kemptm/NCNCA-Lap-Counter/doc/images/Arduino MEGA 2560 Sheet 1.png

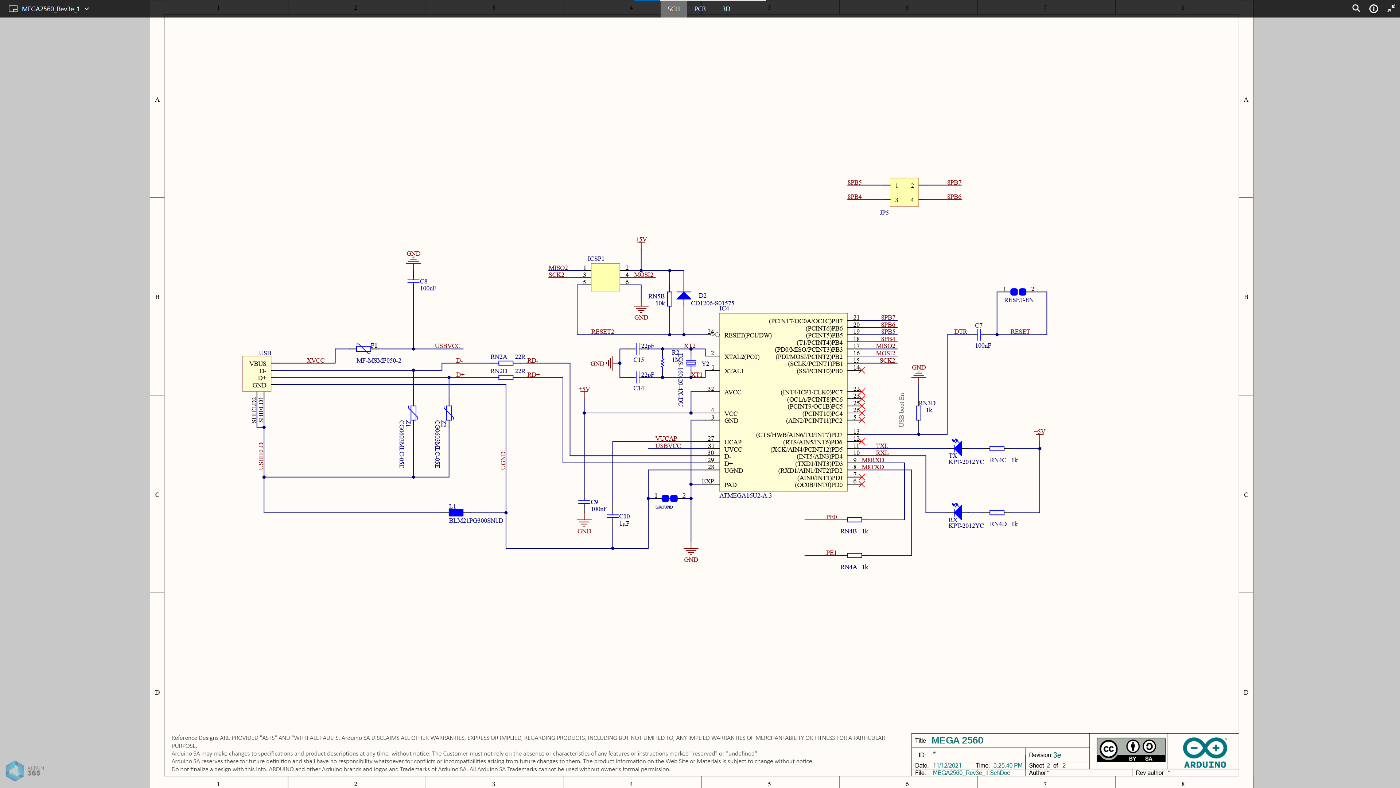
doc/images/Arduino MEGA 2560 Sheet 1.png
