kemptm/NCNCA-Lap-Counter/doc/images/Arduino MEGA 2560 Sheet 2.png

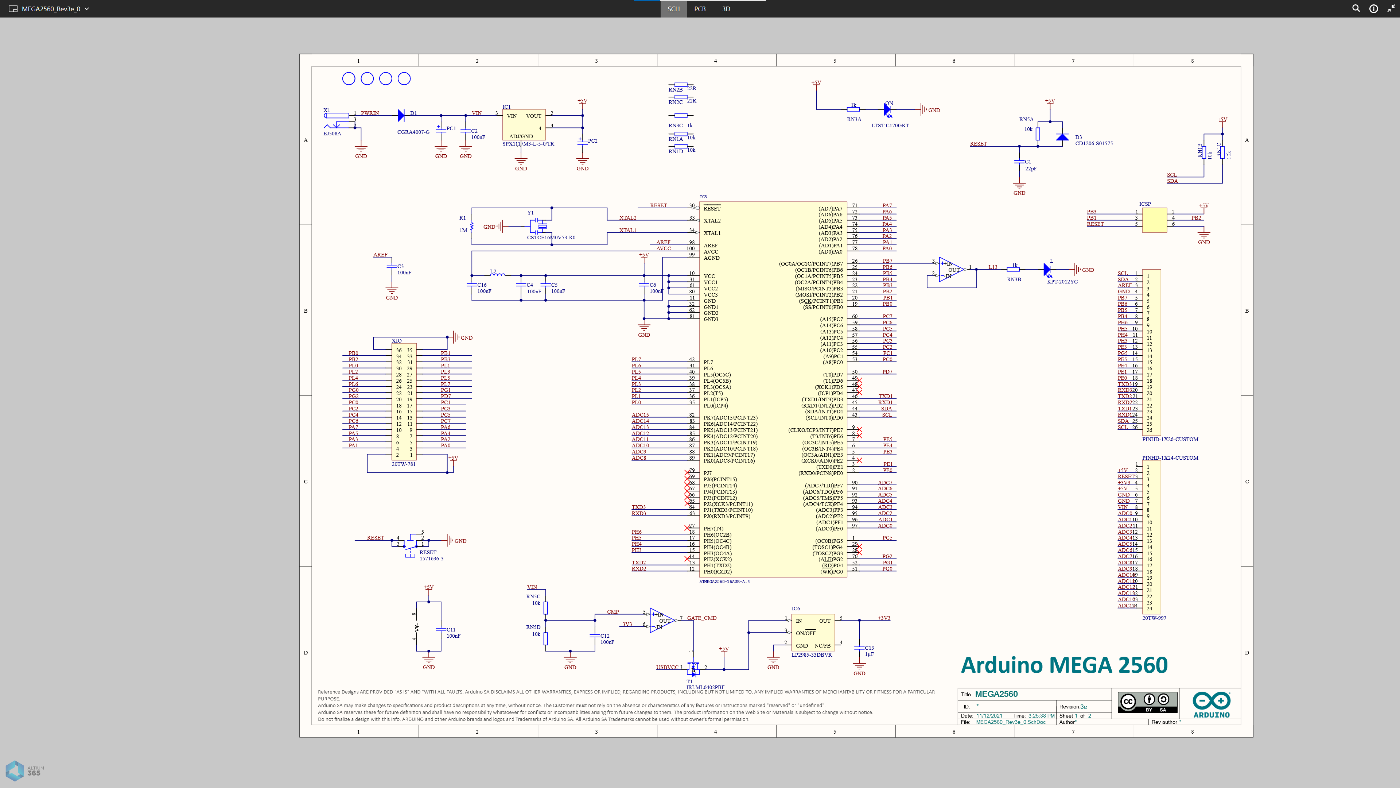
doc/images/Arduino MEGA 2560 Sheet 2.png
