kemptm/NCNCA-Lap-Counter/doc/images/PXL_20230830_222036066.jpg

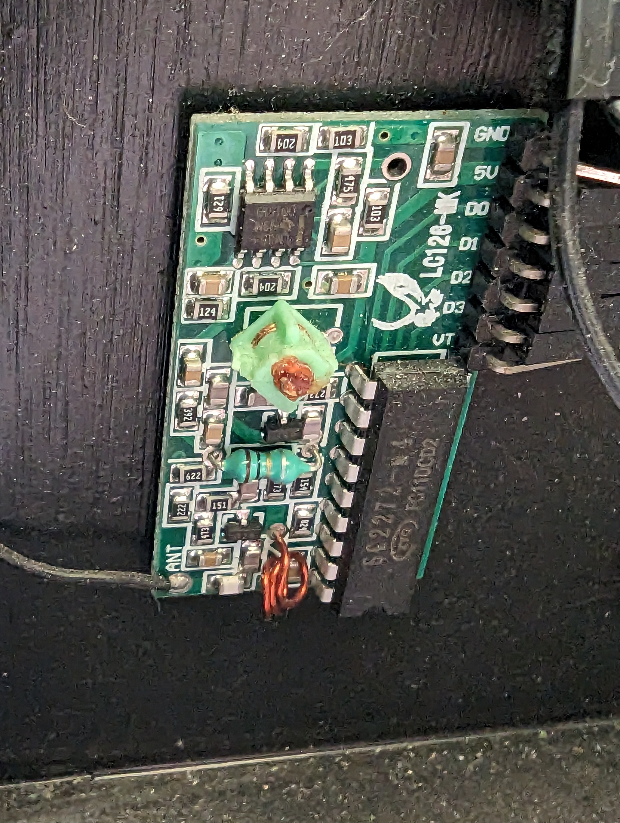
doc/images/PXL_20230830_222036066.jpg
