kemptm/NCNCA-Lap-Counter/doc/images/PXL_20230830_223550689.jpg

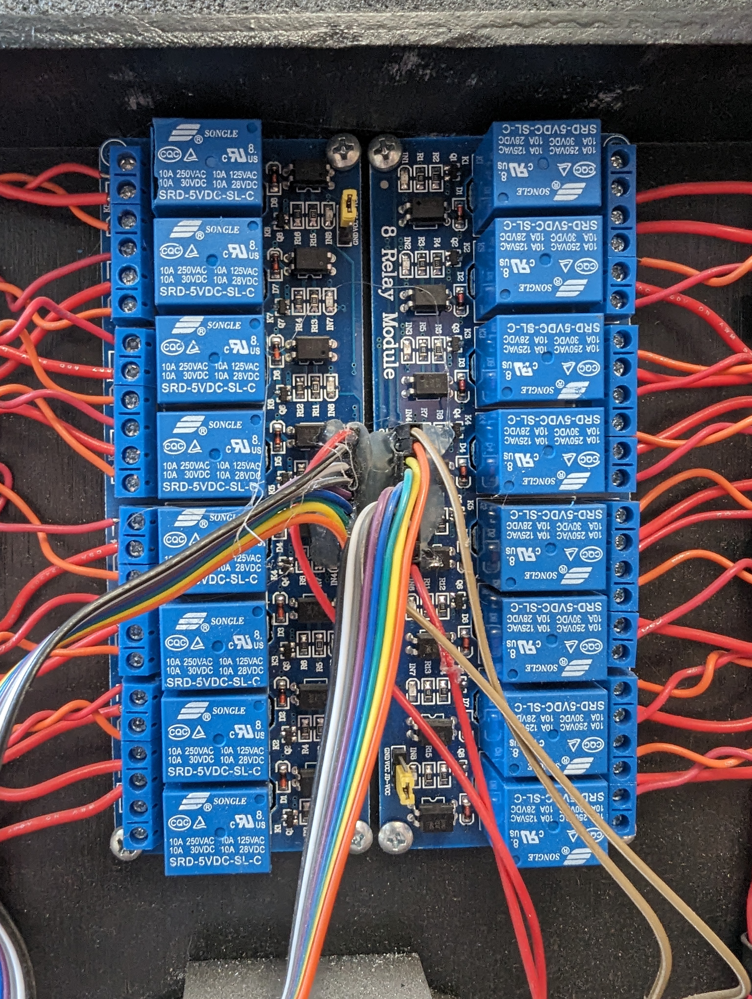
doc/images/PXL_20230830_223550689.jpg
