kemptm/NCNCA-Lap-Counter/doc/images/PXL_20230830_223600172.jpg

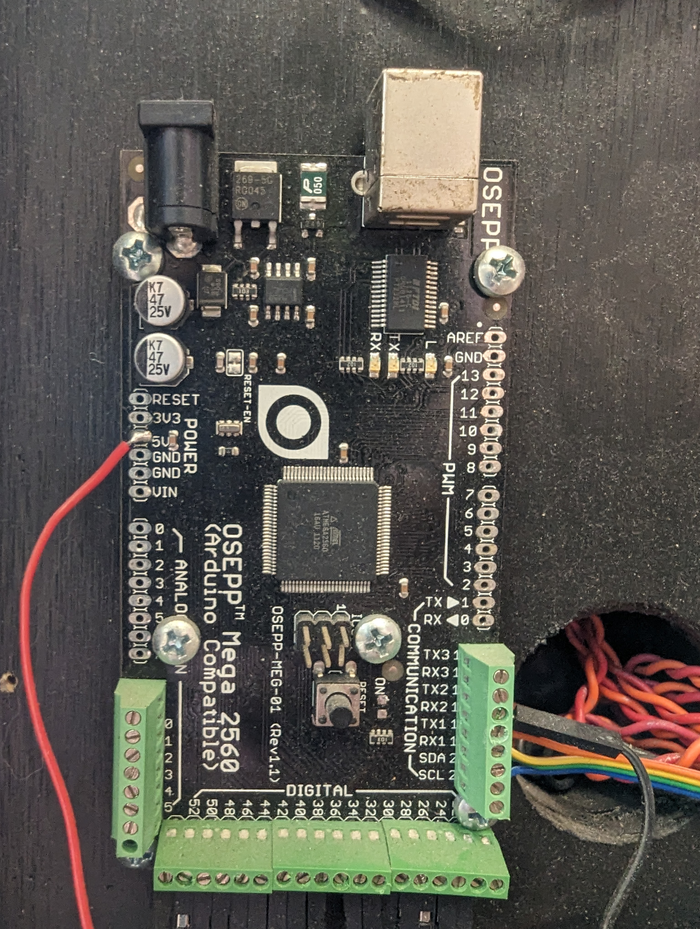
doc/images/PXL_20230830_223600172.jpg
