kemptm/NCNCA-Lap-Counter/doc/images/PXL_20230830_223612654.jpg

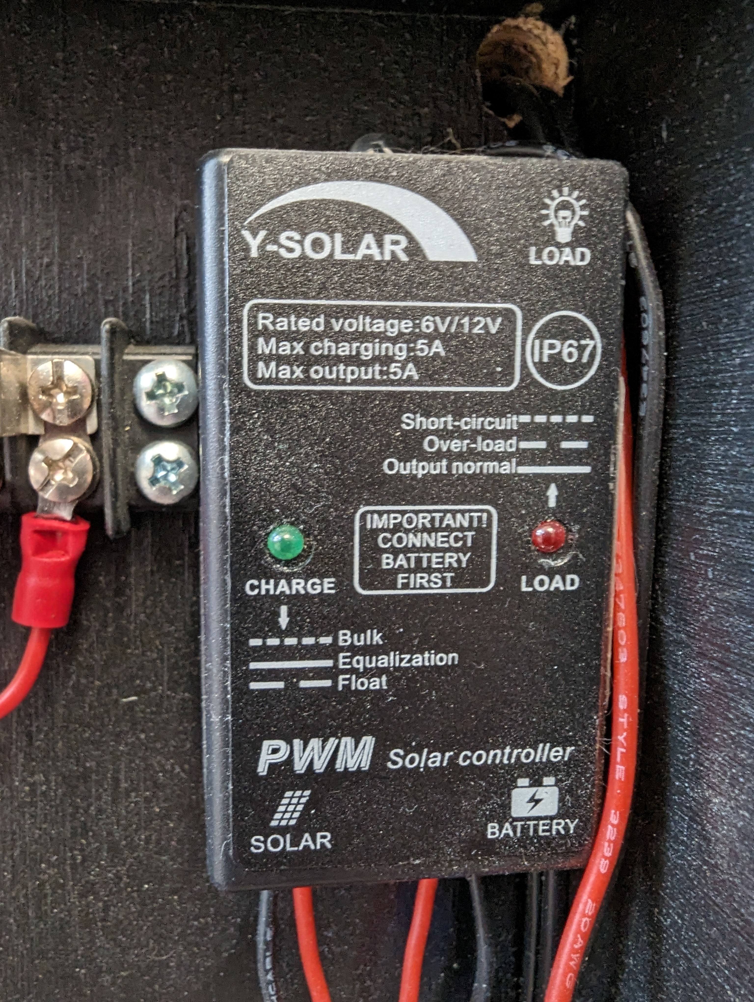
doc/images/PXL_20230830_223612654.jpg
