kemptm/NCNCA-Lap-Counter/doc/images/PXL_20230830_223639269.jpg

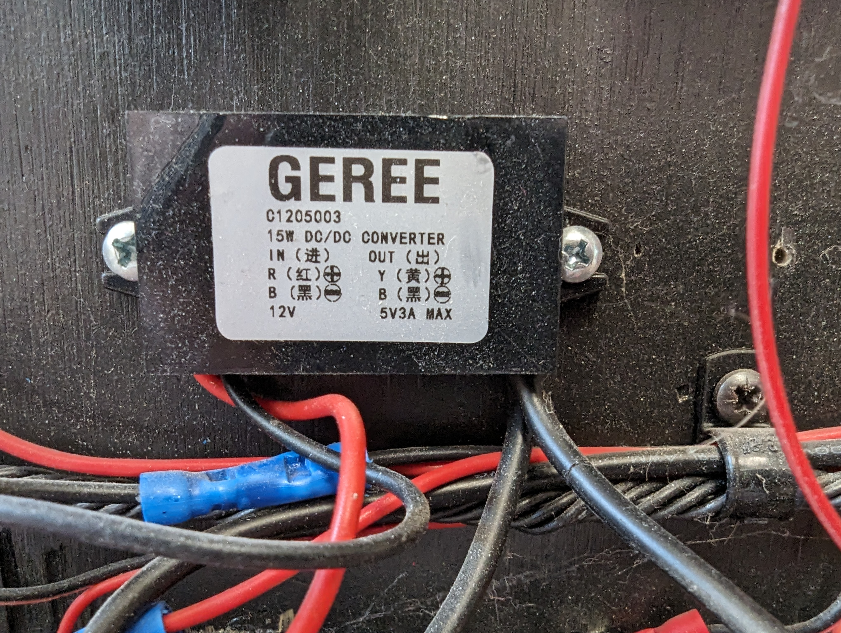
doc/images/PXL_20230830_223639269.jpg
