kemptm/NCNCA-Lap-Counter/mechanical/8-Barrier-Strip.FCStd

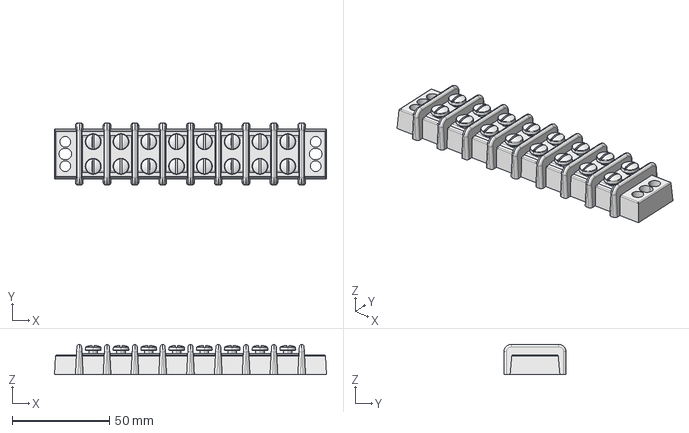
[picture p46: CAD file, 2024-01-13]
mechanical/8-Barrier-Strip.FCStd
139.9 x 32.0 x 15.5 mm
