kemptm/NCNCA-Lap-Counter/mechanical/Flyback-Board.FCStd

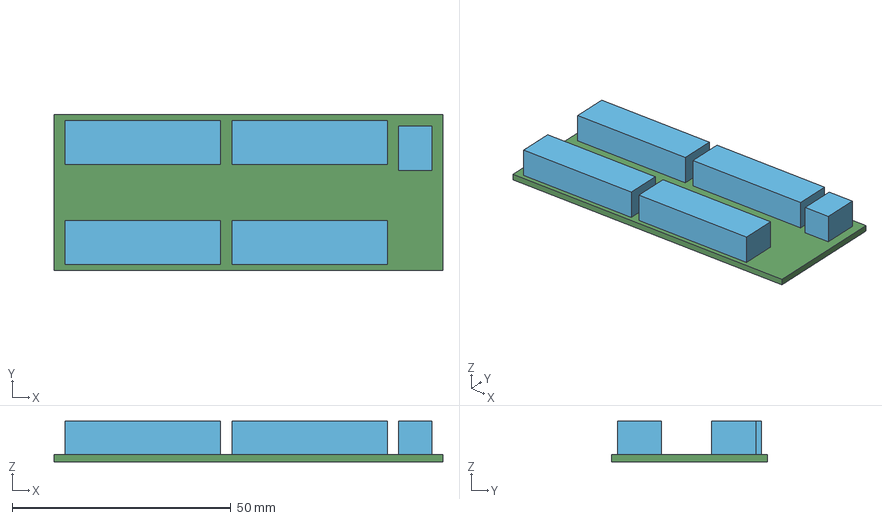
[picture p47: CAD file, 2024-01-13]
mechanical/Flyback-Board.FCStd
88.9 x 35.6 x 9.27 mm
Board
JA2
JB1
JA1
JB2
J3
