kemptm/NCNCA-Lap-Counter/mechanical/6-Barrier-Strip.FCStd

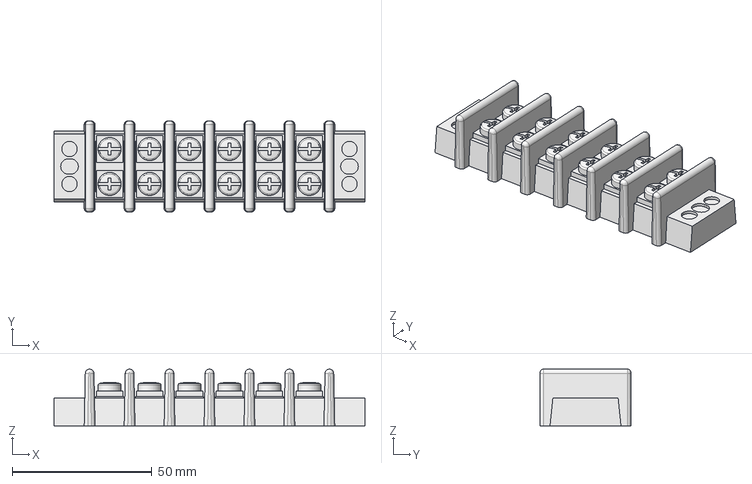
[picture p48: CAD file, 2024-01-13]
mechanical/6-Barrier-Strip.FCStd
111.3 x 32.5 x 20.3 mm
